daparker2/Tinast_Public/doc/Setting up a raspberry pi for automotive_files/image003.png

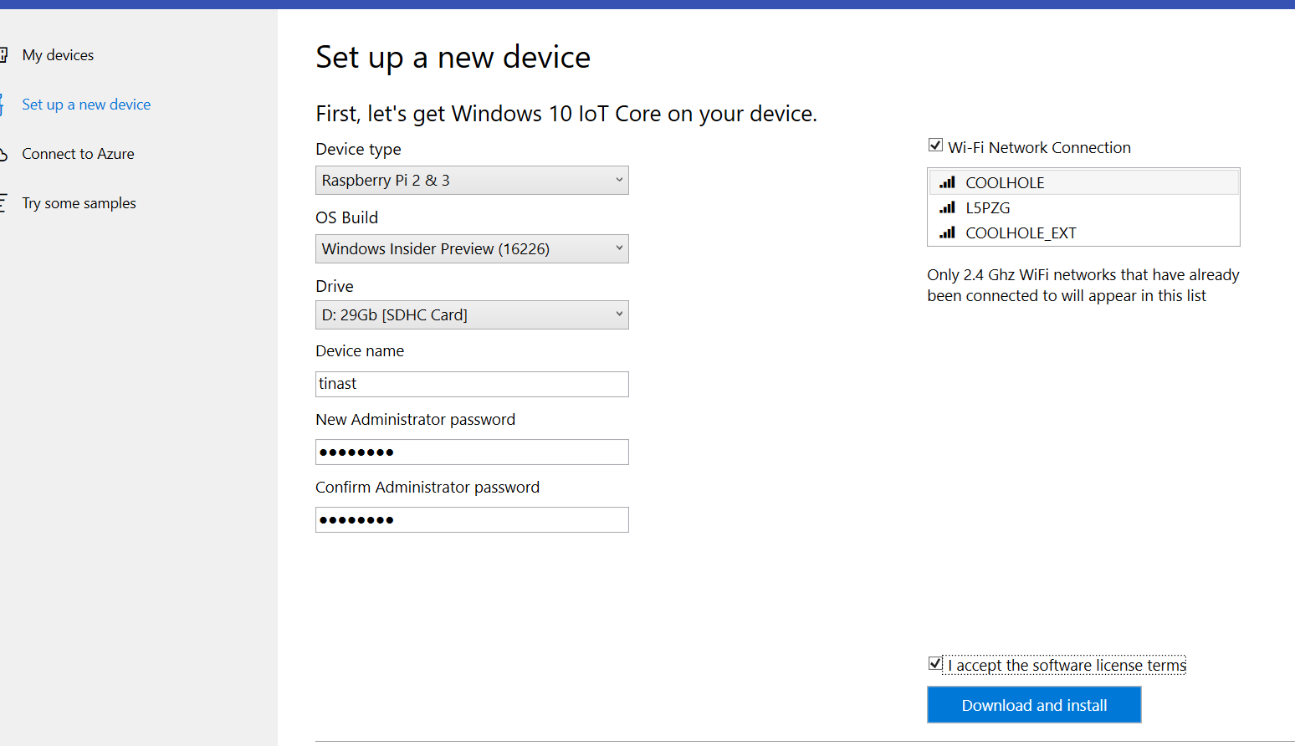
doc/Setting up a raspberry pi for automotive_files/image003.png
