daparker2/Tinast_Public/doc/Setting up a raspberry pi for automotive_files/image010.jpg

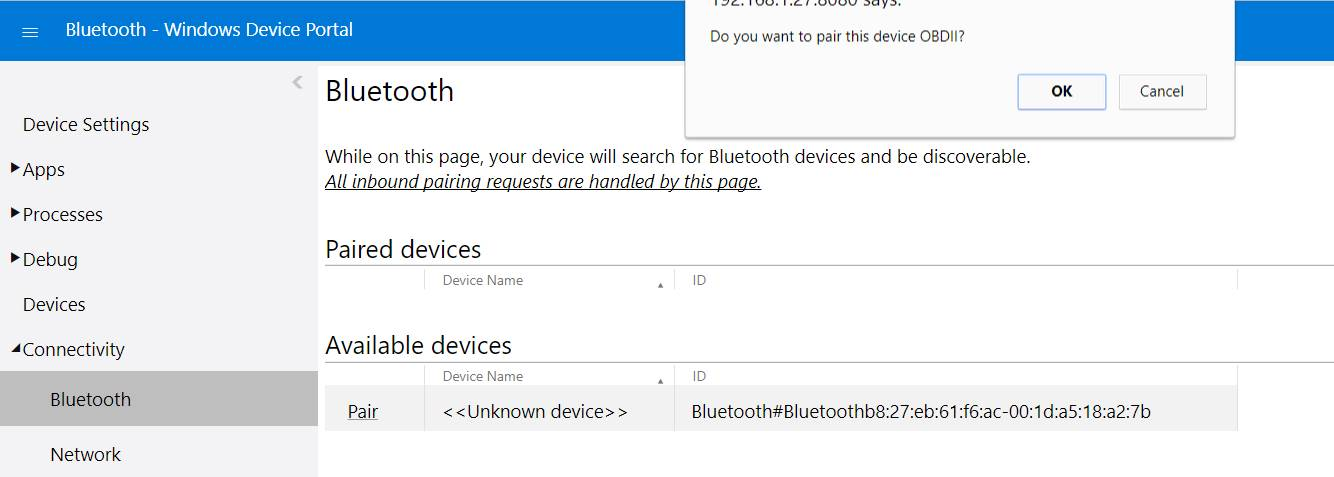
doc/Setting up a raspberry pi for automotive_files/image010.jpg
