daparker2/Tinast_Public/doc/Setting up a raspberry pi for automotive_files/image011.png

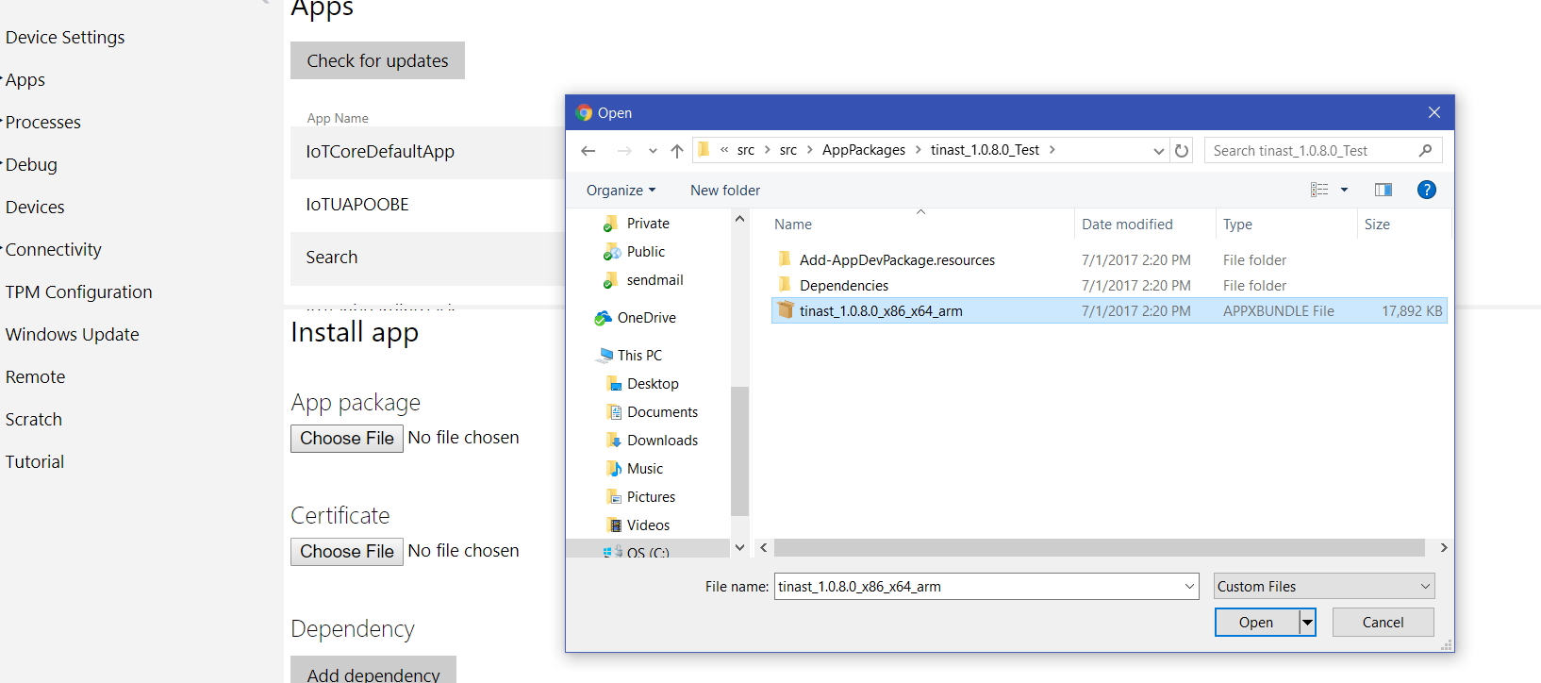
doc/Setting up a raspberry pi for automotive_files/image011.png
