daparker2/Tinast_Public/img/layout.png

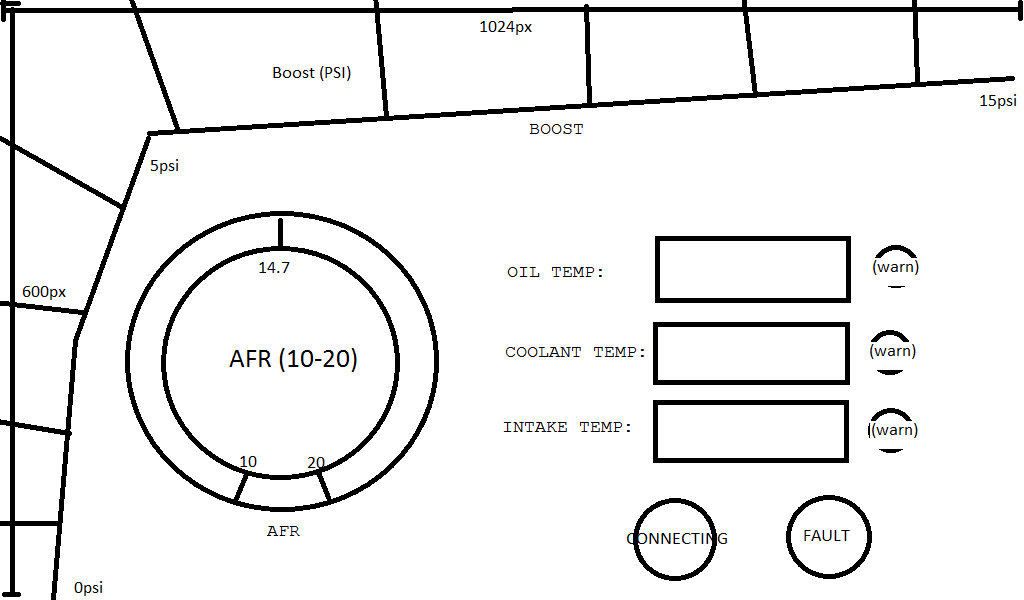
img/layout.png
