daparker2/Tinast_Public/img/proto1.jpg

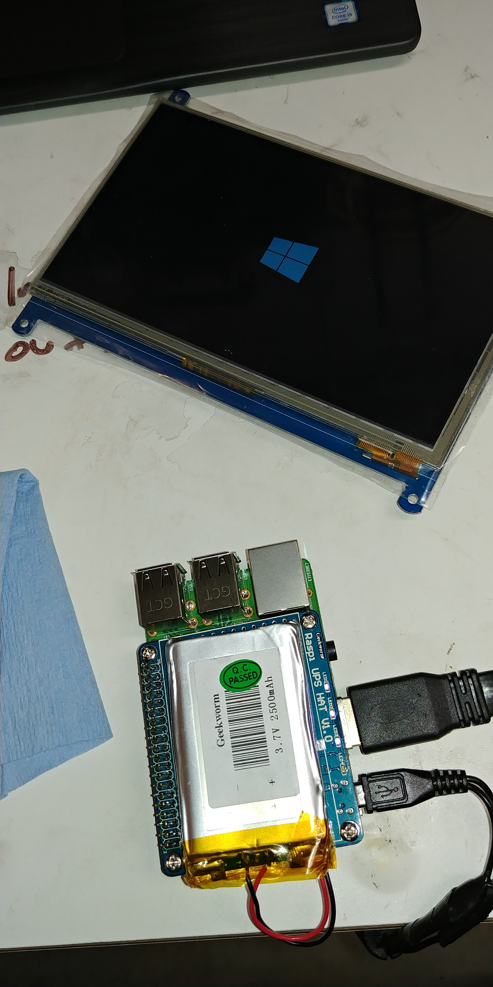
img/proto1.jpg
