daparker2/Tinast_Public/img/Screenshot_2017-08-09_19-23-27.jpg

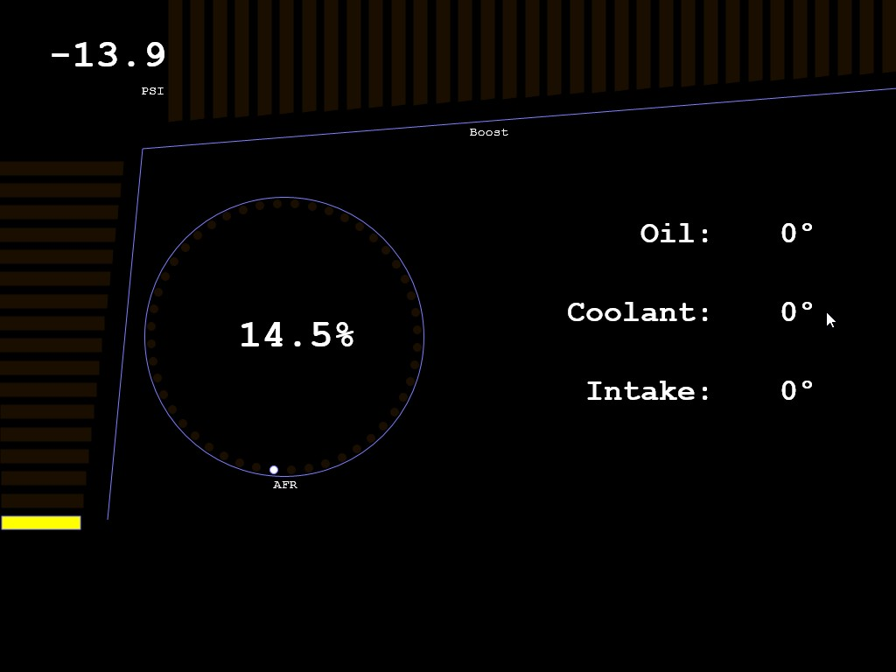
img/Screenshot_2017-08-09_19-23-27.jpg
