daparker2/Tinast_Public/src/tinast/bg.png

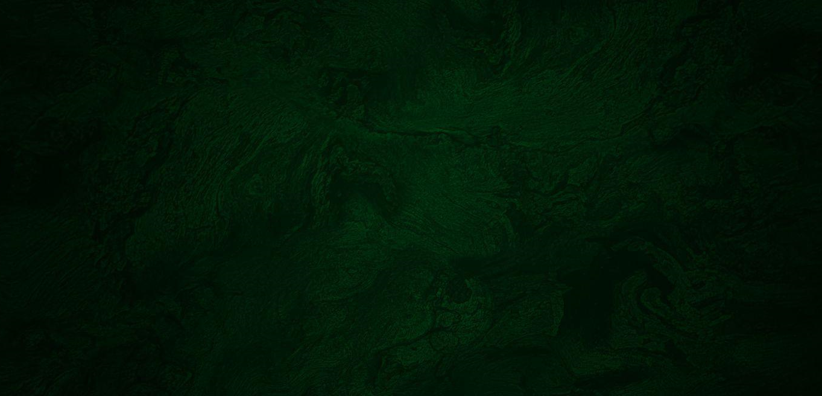
src/tinast/bg.png
